NeoCraftStudio/stream-deck-macro/case/renders/case_v2_top.png

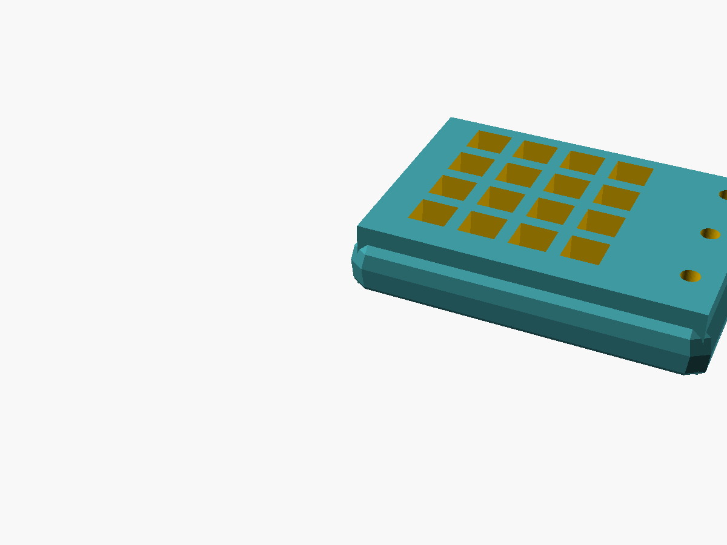
case/renders/case_v2_top.png
