NeoCraftStudio/stream-deck-macro/case/renders/case_v3_top.png

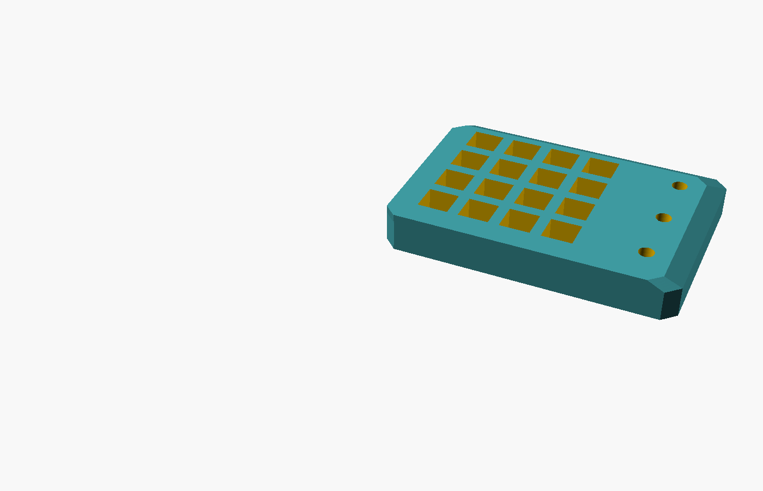
case/renders/case_v3_top.png
