NeoCraftStudio/stream-deck-macro/case/renders/case_v4_bottom_alone.png

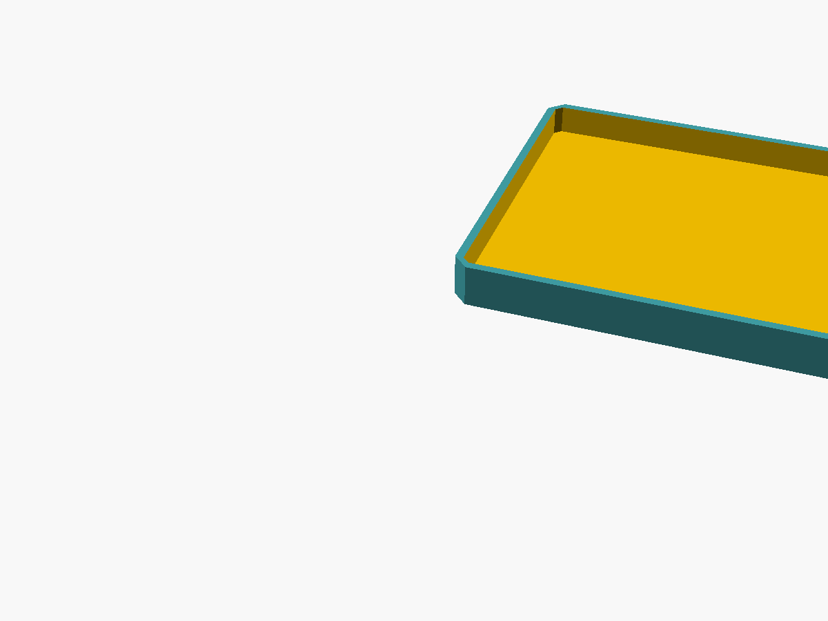
case/renders/case_v4_bottom_alone.png
