NeoCraftStudio/stream-deck-macro/case/renders/case_v5_riser_elevation.png

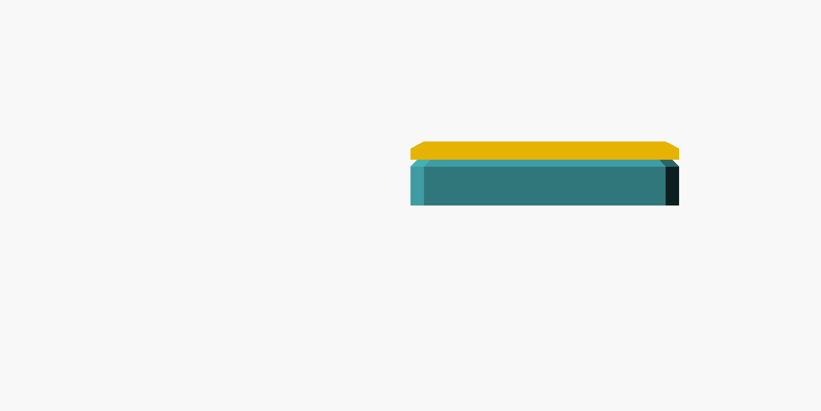
case/renders/case_v5_riser_elevation.png
