NeoCraftStudio/stream-deck-macro/case/renders/case_v5_riser_zoom.png

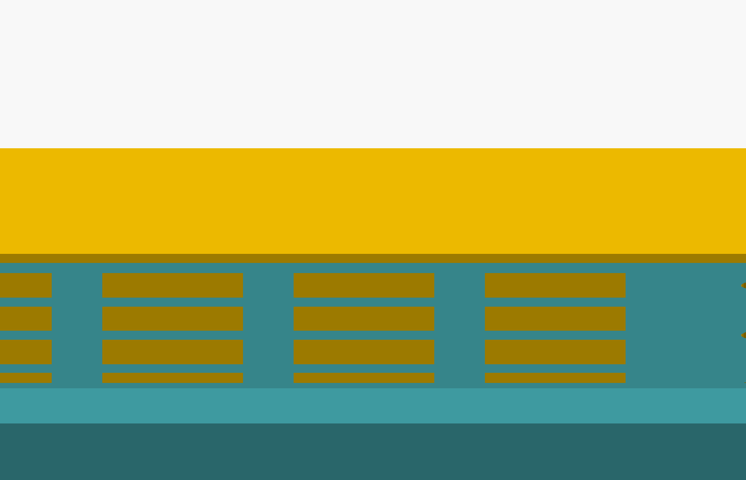
case/renders/case_v5_riser_zoom.png
