NeoCraftStudio/stream-deck-macro/case/renders/ocreeb_top_original.png

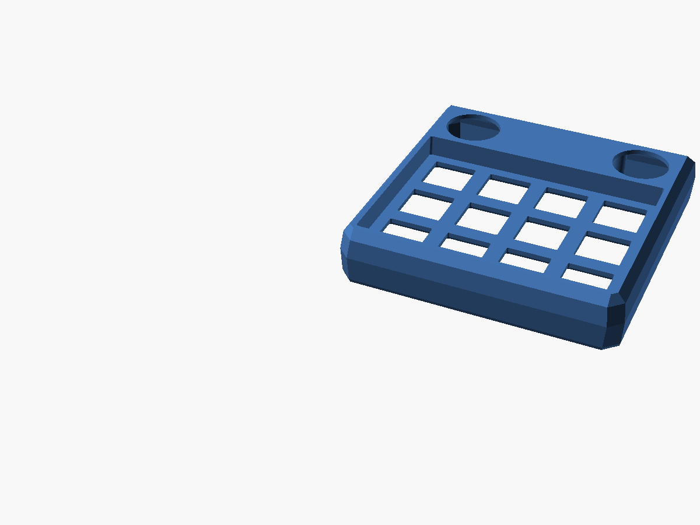
case/renders/ocreeb_top_original.png
