NeoCraftStudio/stream-deck-macro/case/renders/plate_v1.png

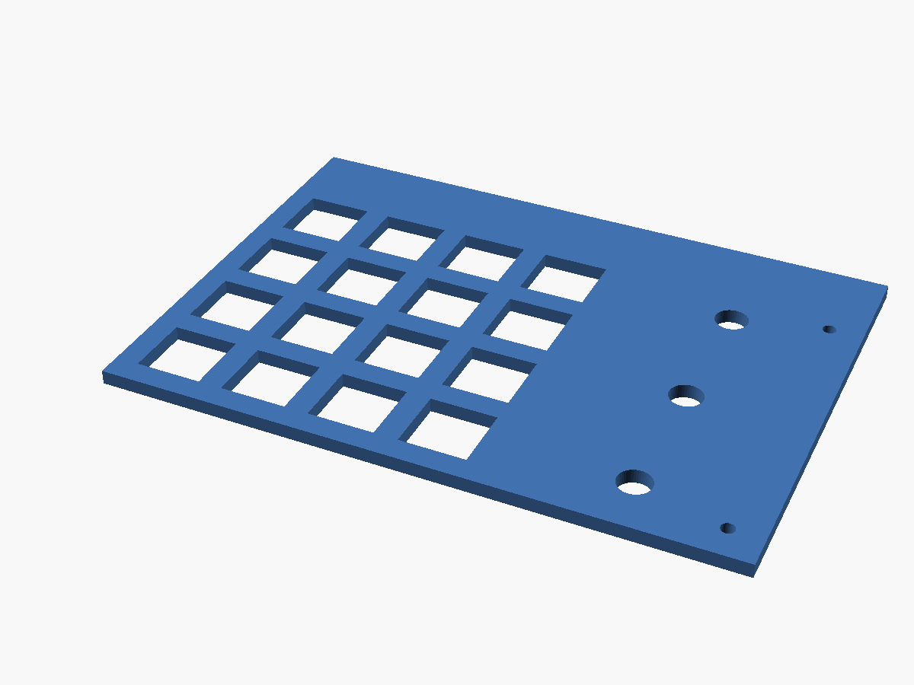
case/renders/plate_v1.png
