NeoCraftStudio/stream-deck-macro/case/view_ocreeb_bottom.scad

import("reference/Case_Bottom.stl");
