NeoCraftStudio/stream-deck-macro/case/view_ocreeb_top.scad

import("reference/Case_Top.stl");
