NeoCraftStudio/stream-deck-macro/case/renders/debug1.png

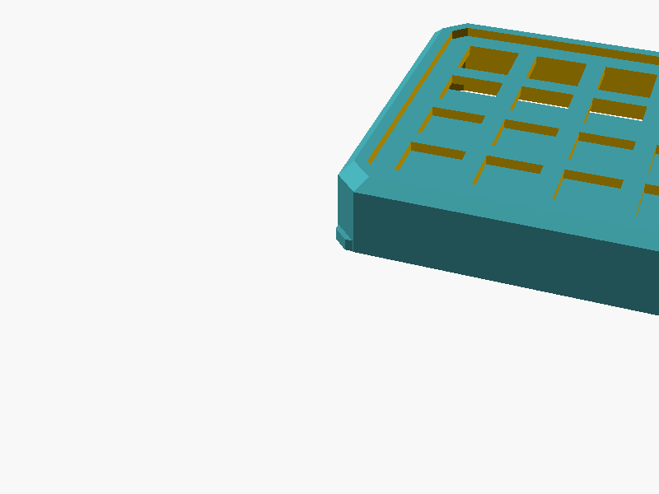
case/renders/debug1.png
